liveboxandy/ZX-Spectrum-48K-Issue-3B---Based-on-Gerbers-by-PABB-on-PCBWay/STPS/CONN-TH_5P-P2.54_520315-5.step

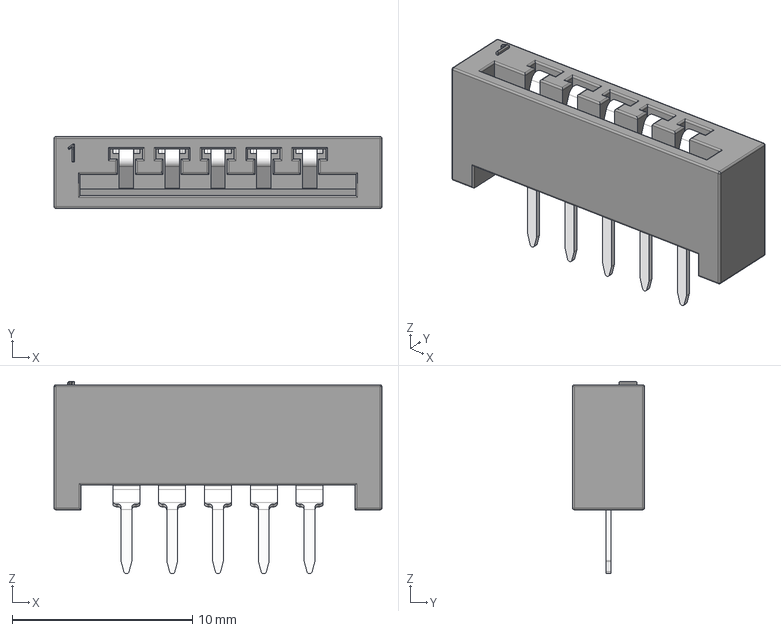
[picture p18: CAD file, 2026-09-27]
STPS/CONN-TH_5P-P2.54_520315-5.step
18.2 x 4.00 x 10.7 mm
Pins
Connector Body
