liveboxandy/ZX-Spectrum-48K-Issue-3B---Based-on-Gerbers-by-PABB-on-PCBWay/STPS/NS_LM1889N.step

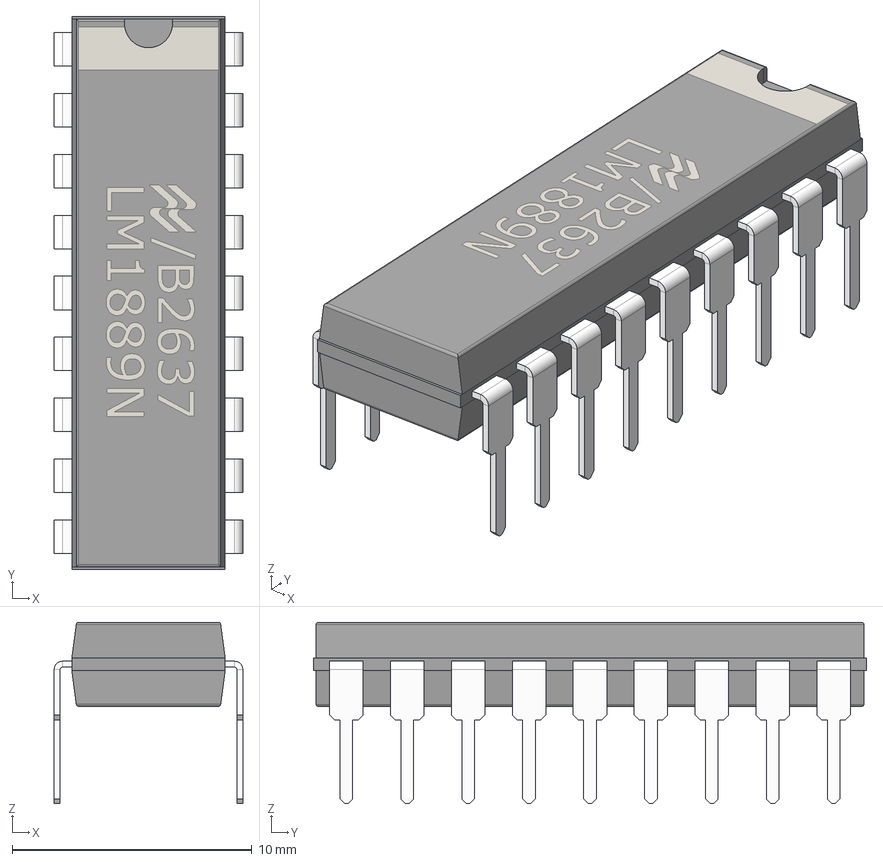
[picture p19: CAD file, 2026-09-27]
STPS/NS_LM1889N.step
7.87 x 23.1 x 7.57 mm
Basic - DIP 7.62 v3
DIP Pin 14-20 v3
DIP Pin 14-20 v3(Mirror)
