liveboxandy/ZX-Spectrum-48K-Issue-3B---Based-on-Gerbers-by-PABB-on-PCBWay/STPS/xAxial Capacitor.step

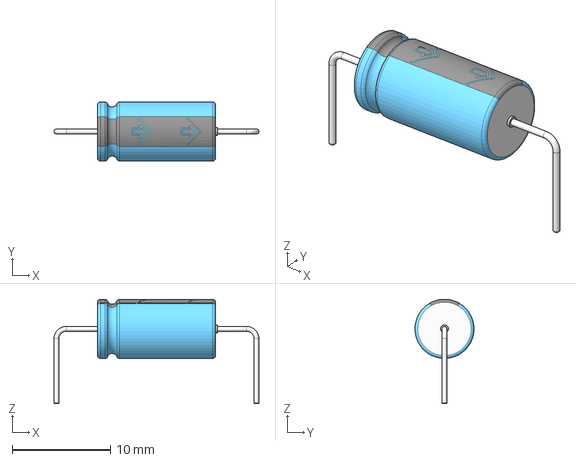
[picture p20: CAD file, 2026-09-27]
STPS/xAxial Capacitor.step
20.8 x 5.99 x 10.6 mm
