liveboxandy/ZX-Spectrum-48K-Issue-3B---Based-on-Gerbers-by-PABB-on-PCBWay/STPS/DO-35_3.90x1.90x0.60x10.16.STEP

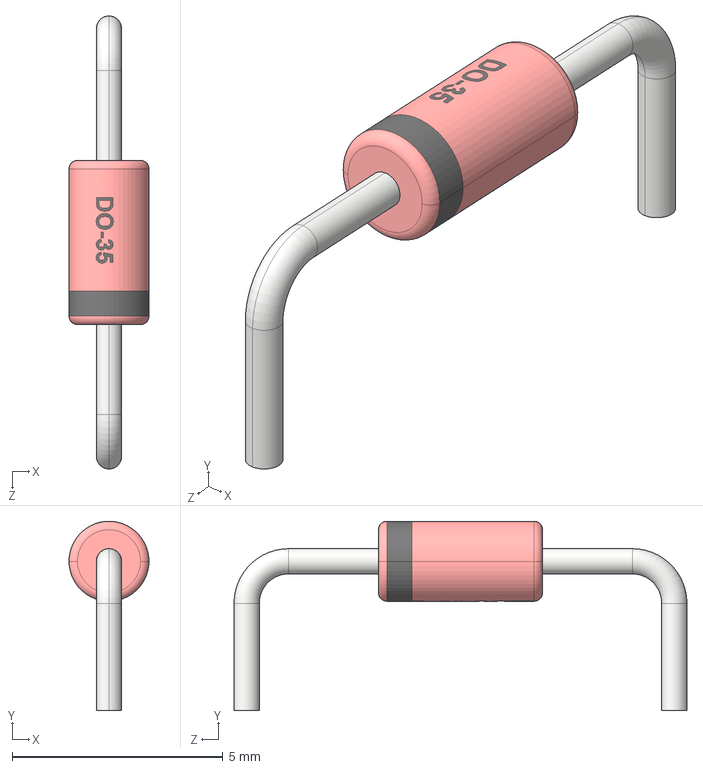
[picture p21: CAD file, 2026-09-27]
STPS/DO-35_3.90x1.90x0.60x10.16.STEP
1.90 x 4.50 x 10.8 mm
