liveboxandy/ZX-Spectrum-48K-Issue-3B---Based-on-Gerbers-by-PABB-on-PCBWay/STPS/DIP-24_W10.16mm_Socket.step

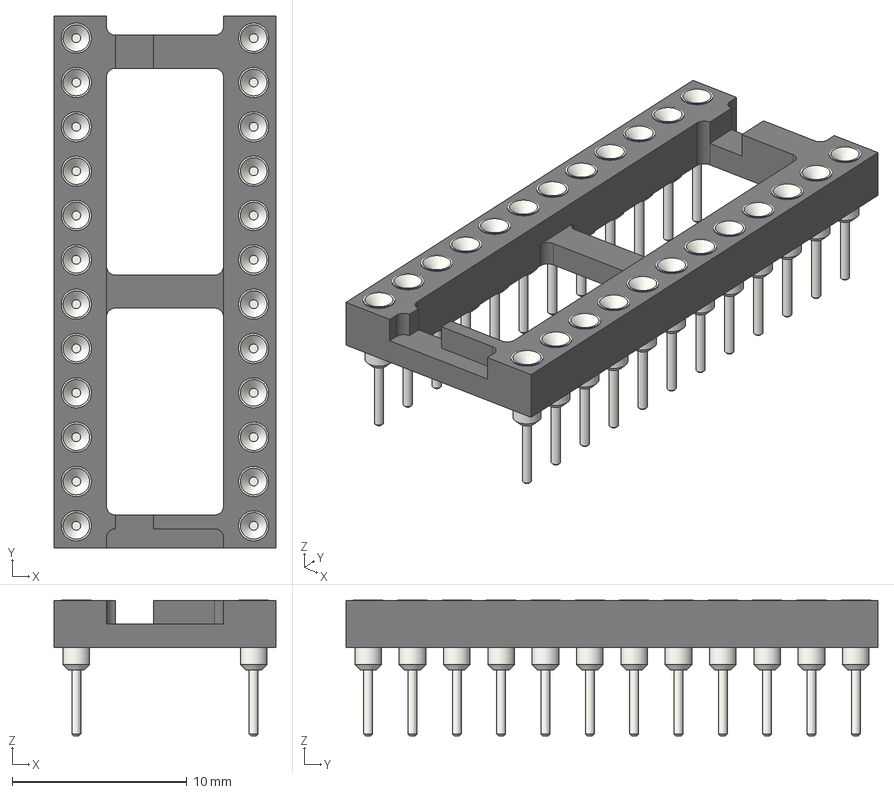
[picture p22: CAD file, 2026-09-27]
STPS/DIP-24_W10.16mm_Socket.step
12.7 x 30.5 x 7.79 mm
