liveboxandy/ZX-Spectrum-48K-Issue-3B---Based-on-Gerbers-by-PABB-on-PCBWay/STPS/Capacitor Ceramic No Polarity axial 22.86.STEP

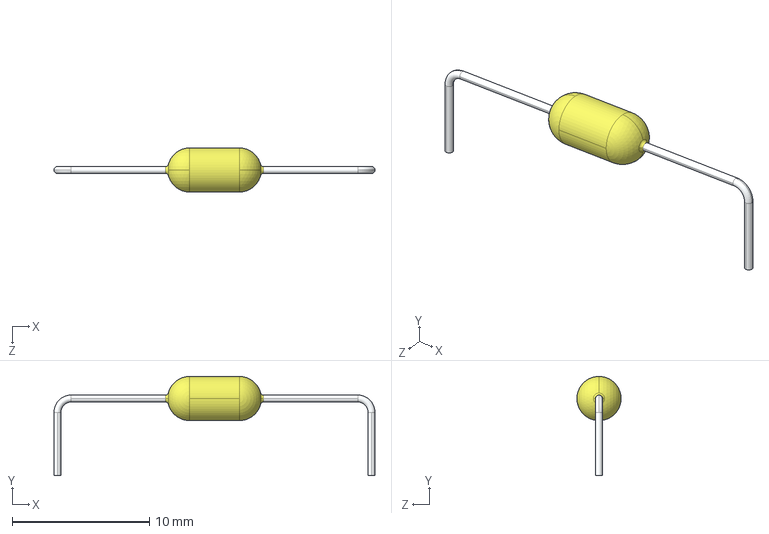
[picture p23: CAD file, 2026-09-27]
STPS/Capacitor Ceramic No Polarity axial 22.86.STEP
23.4 x 7.22 x 3.22 mm
