liveboxandy/ZX-Spectrum-48K-Issue-3B---Based-on-Gerbers-by-PABB-on-PCBWay/STPS/R_Axial_DIN0309_L9.0mm_D3.2mm_P12.70mm_Horizontal.step

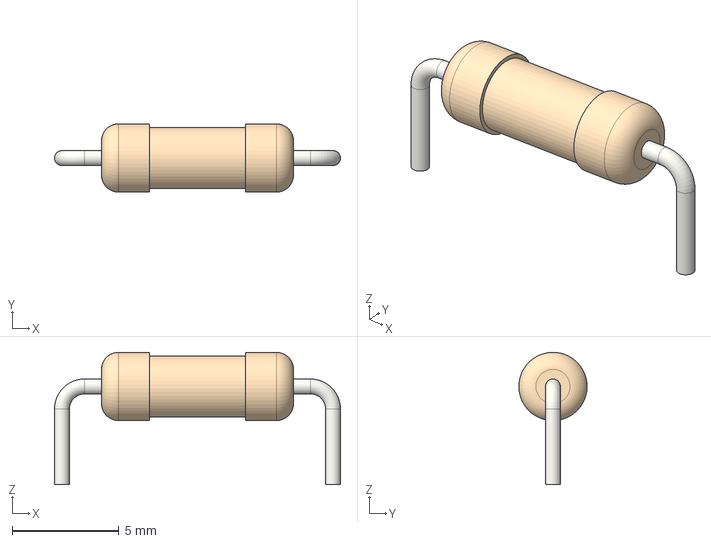
[picture p24: CAD file, 2026-09-27]
STPS/R_Axial_DIN0309_L9.0mm_D3.2mm_P12.70mm_Horizontal.step
13.4 x 3.20 x 6.20 mm
