liveboxandy/ZX-Spectrum-48K-Issue-3B---Based-on-Gerbers-by-PABB-on-PCBWay/STPS/409HS-1K.stp

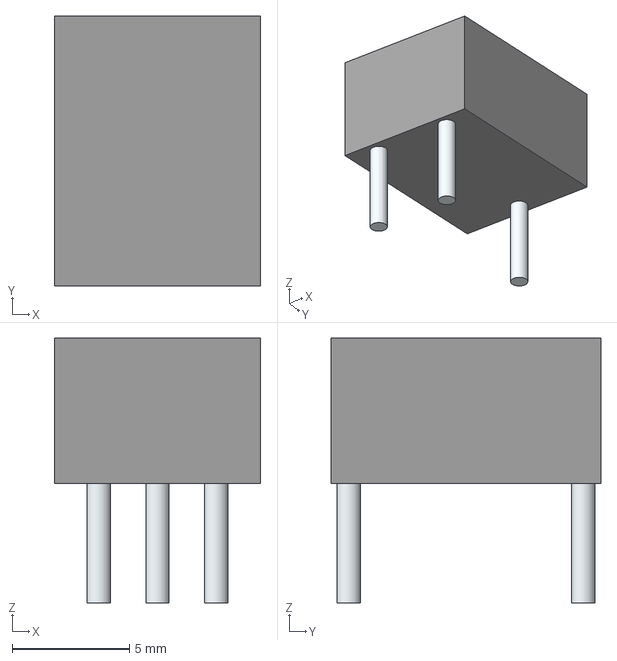
[picture p26: CAD file, 2026-09-27]
STPS/409HS-1K.stp
8.80 x 11.5 x 11.3 mm
Leads
