liveboxandy/ZX-Spectrum-48K-Issue-3B---Based-on-Gerbers-by-PABB-on-PCBWay/STPS/Resistor-0207-6.3x2.4x25.40.STEP

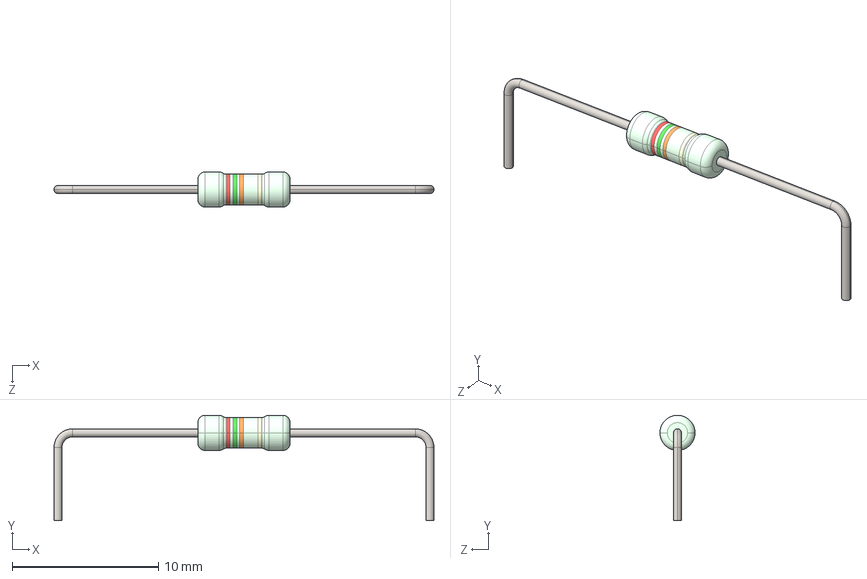
[picture p29: CAD file, 2026-09-27]
STPS/Resistor-0207-6.3x2.4x25.40.STEP
26.0 x 7.20 x 2.40 mm
