liveboxandy/ZX-Spectrum-48K-Issue-3B---Based-on-Gerbers-by-PABB-on-PCBWay/STPS/5-520315-5.stp

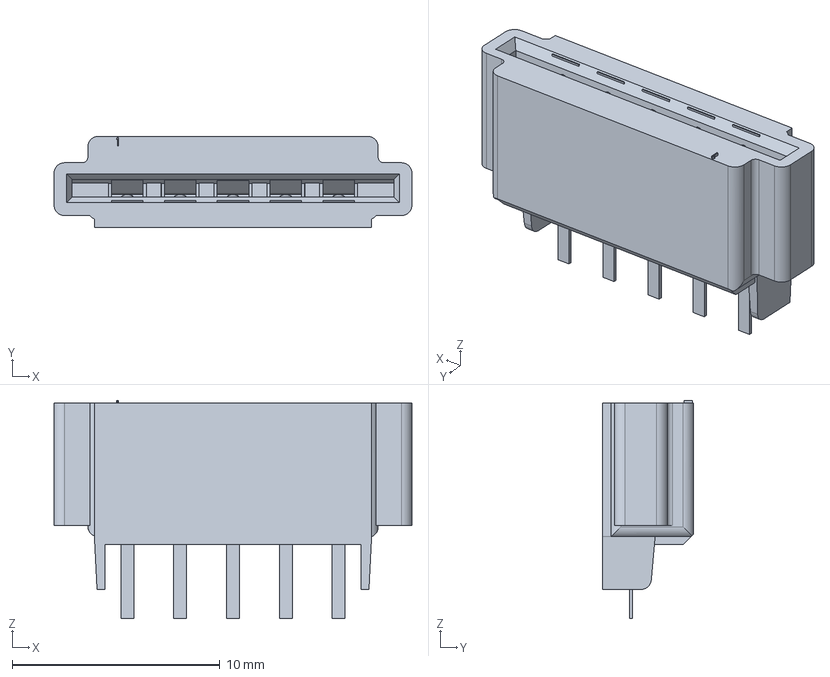
[picture p30: CAD file, 2026-09-27]
STPS/5-520315-5.stp
17.2 x 4.39 x 10.5 mm
