liveboxandy/ZX-Spectrum-48K-Issue-3B---Based-on-Gerbers-by-PABB-on-PCBWay/STPS/STC_4116.step

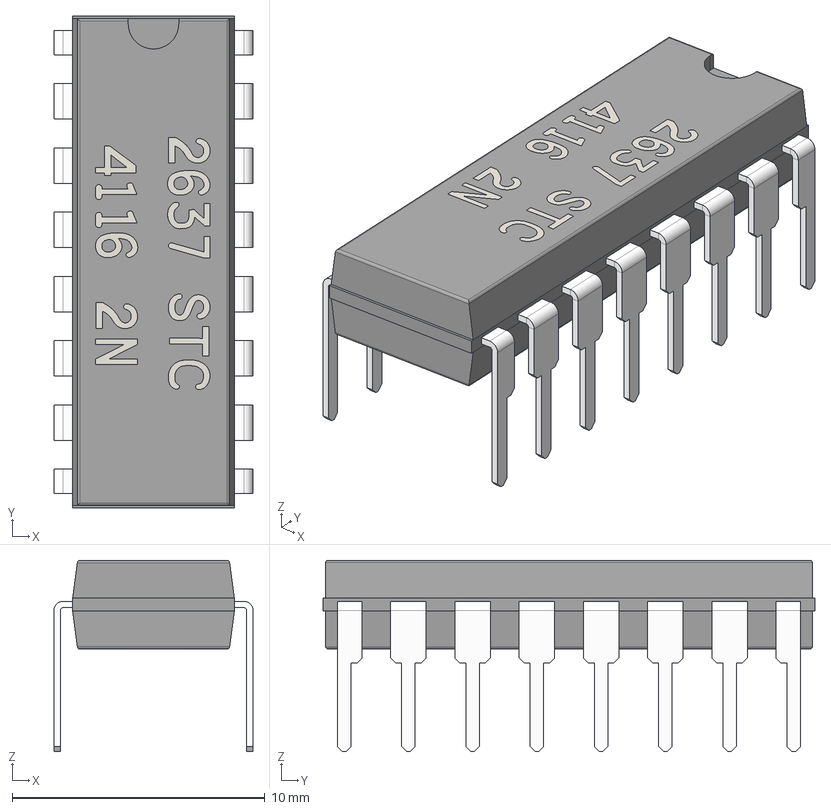
[picture p31: CAD file, 2026-09-27]
STPS/STC_4116.step
7.87 x 19.5 x 7.57 mm
Basic - DIP 7.62 v3
DIP Pin 14-20 v3
DIP Pin 14-20 v3(Mirror)
