liveboxandy/ZX-Spectrum-48K-Issue-3B---Based-on-Gerbers-by-PABB-on-PCBWay/STPS/CONN_5-520315-8_TYC.stp

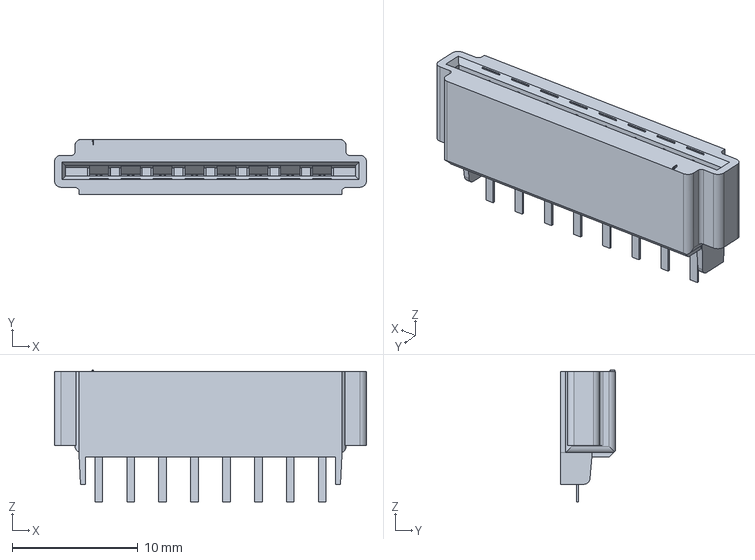
[picture p33: CAD file, 2026-09-27]
STPS/CONN_5-520315-8_TYC.stp
24.8 x 4.39 x 10.5 mm
