liveboxandy/ZX-Spectrum-48K-Issue-3B---Based-on-Gerbers-by-PABB-on-PCBWay/STPS/DO-35_3.90x1.90x0.60x22.86.STEP

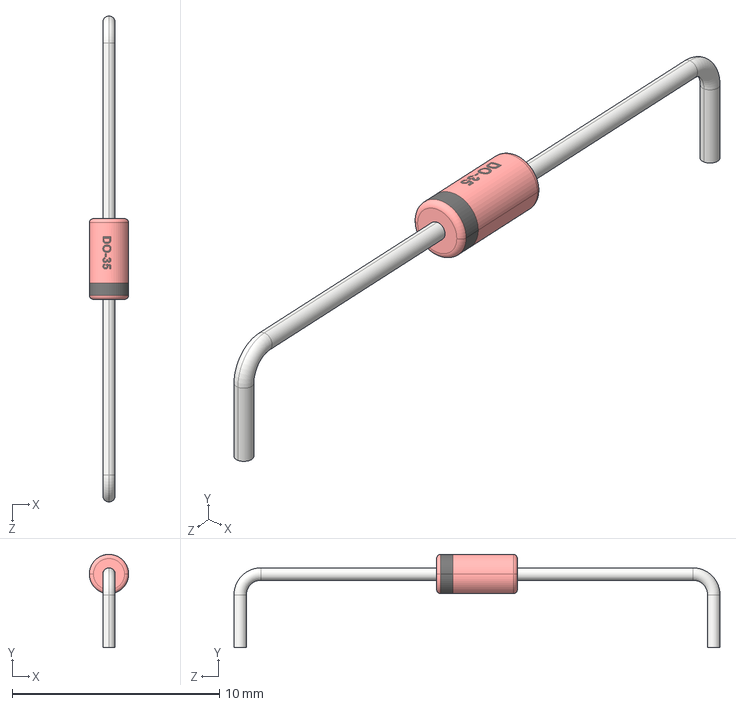
[picture p34: CAD file, 2026-09-27]
STPS/DO-35_3.90x1.90x0.60x22.86.STEP
1.90 x 4.50 x 23.5 mm
