liveboxandy/ZX-Spectrum-48K-Issue-3B---Based-on-Gerbers-by-PABB-on-PCBWay/STPS/Capacitor Ceramic No Polarity axial 10.16.STEP

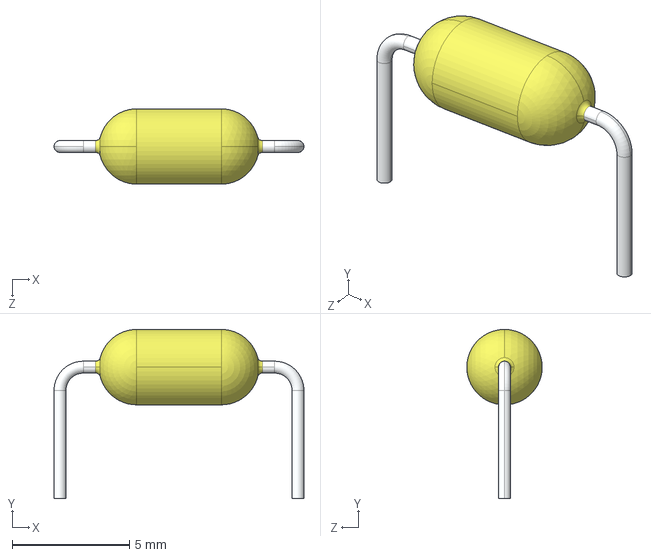
[picture p36: CAD file, 2026-09-27]
STPS/Capacitor Ceramic No Polarity axial 10.16.STEP
10.7 x 7.22 x 3.22 mm
