liveboxandy/ZX-Spectrum-48K-Issue-3B---Based-on-Gerbers-by-PABB-on-PCBWay/STPS/FCR1281 S6A 6mm.stp

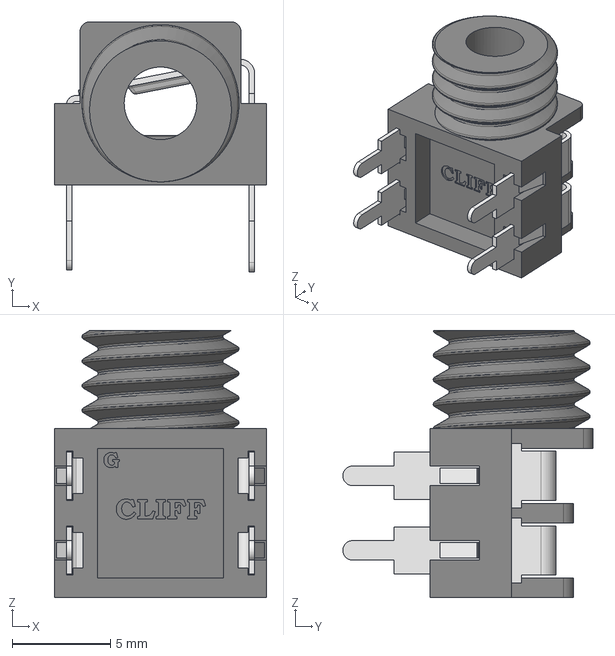
[picture p37: CAD file, 2026-09-27]
STPS/FCR1281 S6A 6mm.stp
10.8 x 12.8 x 13.6 mm
