liveboxandy/ZX-Spectrum-48K-Issue-3B---Based-on-Gerbers-by-PABB-on-PCBWay/STPS/DC Power Connector FC68148_20DC10A_202.1mm.STP

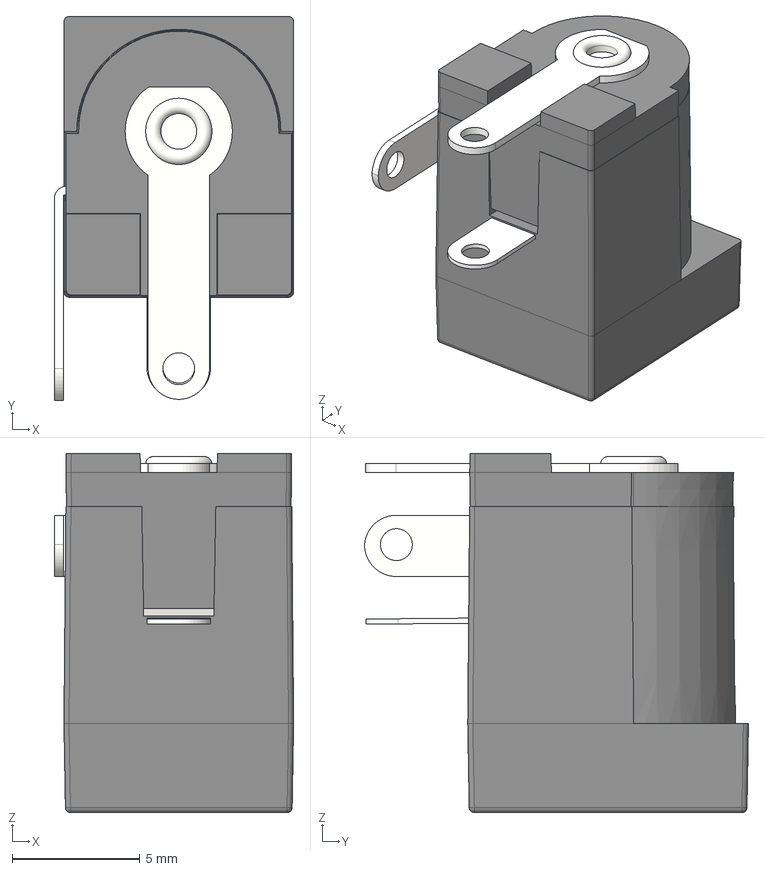
[picture p40: CAD file, 2026-09-27]
STPS/DC Power Connector FC68148_20DC10A_202.1mm.STP
9.37 x 15.0 x 14.1 mm
