liveboxandy/ZX-Spectrum-48K-Issue-3B---Based-on-Gerbers-by-PABB-on-PCBWay/STPS/DO-41-5.10x2.60x12.40.STEP

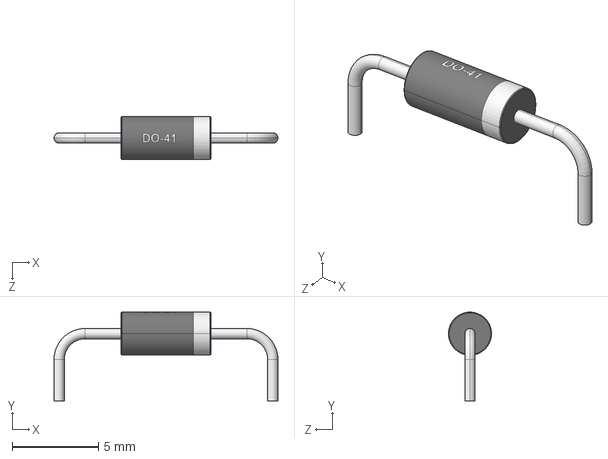
[picture p41: CAD file, 2026-09-27]
STPS/DO-41-5.10x2.60x12.40.STEP
13.0 x 5.15 x 2.50 mm
