liveboxandy/ZX-Spectrum-48K-Issue-3B---Based-on-Gerbers-by-PABB-on-PCBWay/STPS/Resistor-0414-11.5x4.5x25.40.STEP

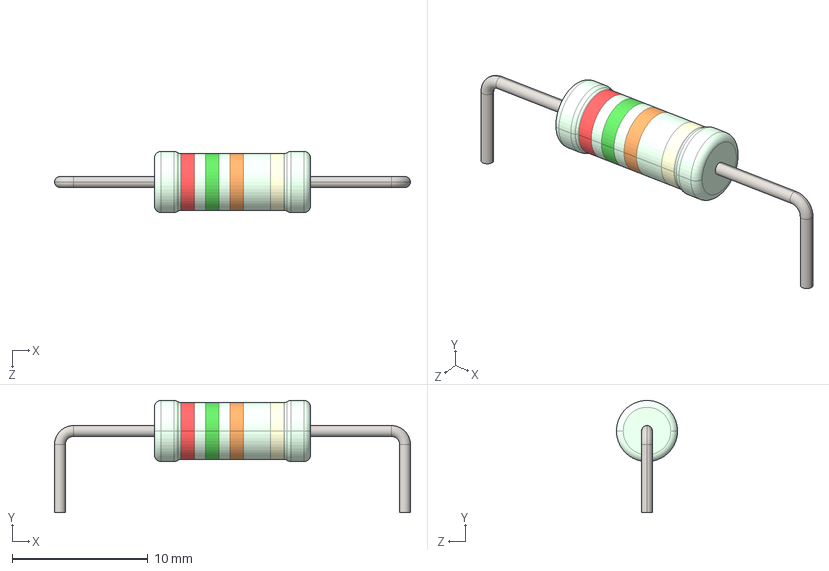
[picture p45: CAD file, 2026-09-27]
STPS/Resistor-0414-11.5x4.5x25.40.STEP
26.2 x 8.25 x 4.50 mm
