liveboxandy/ZX-Spectrum-48K-Issue-3B---Based-on-Gerbers-by-PABB-on-PCBWay/STPS/CP 13x5x0.5x17.78.STEP

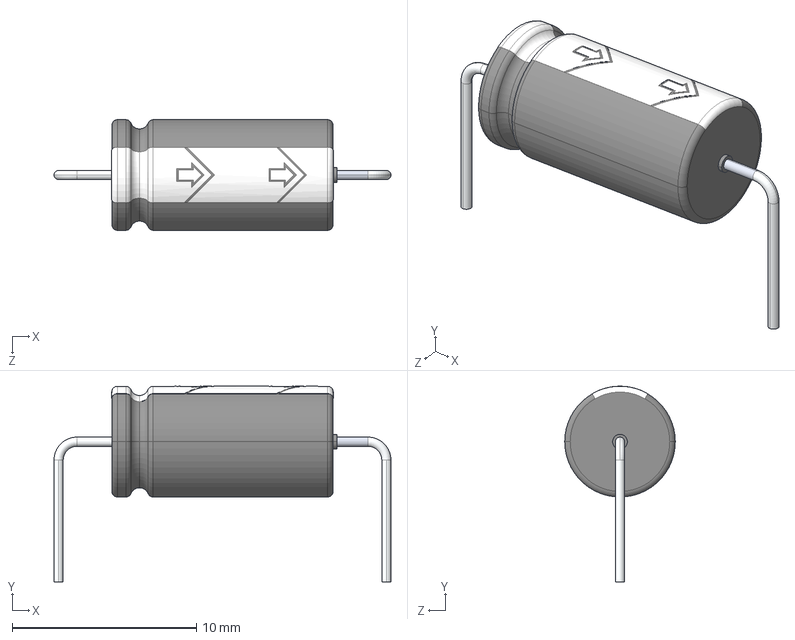
[picture p46: CAD file, 2026-09-27]
STPS/CP 13x5x0.5x17.78.STEP
18.3 x 10.6 x 6.00 mm
