liveboxandy/ZX-Spectrum-48K-Issue-3B---Based-on-Gerbers-by-PABB-on-PCBWay/STPS/Capacitor Ceramic No Polarity axial 17.72.STEP

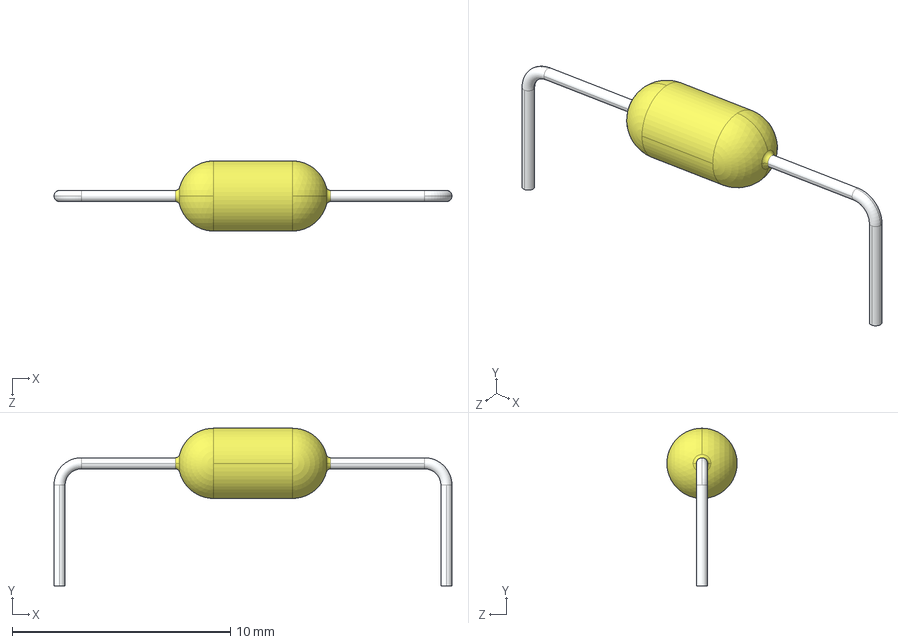
[picture p47: CAD file, 2026-09-27]
STPS/Capacitor Ceramic No Polarity axial 17.72.STEP
18.2 x 7.22 x 3.22 mm
