liveboxandy/ZX-Spectrum-48K-Issue-3B---Based-on-Gerbers-by-PABB-on-PCBWay/STPS/COIL_L1.step

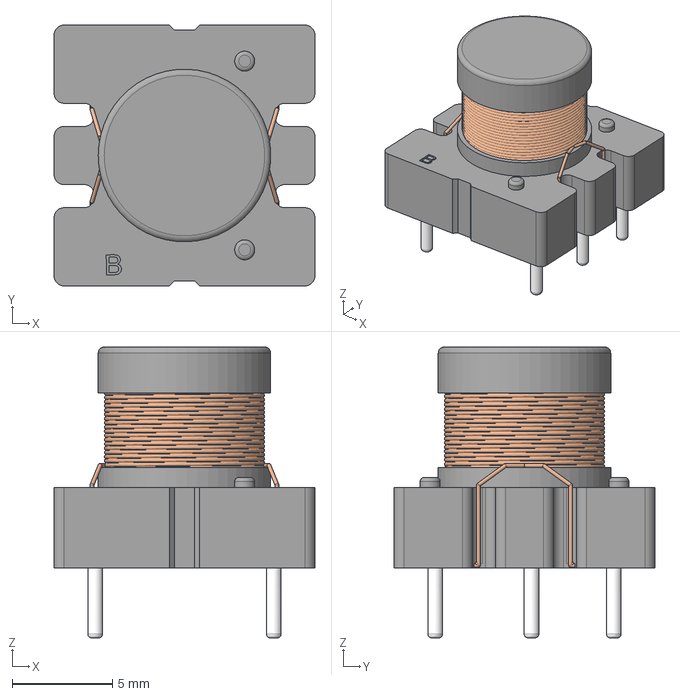
[picture p49: CAD file, 2026-09-27]
STPS/COIL_L1.step
13.0 x 13.0 x 14.5 mm
