liveboxandy/ZX-Spectrum-48K-Issue-3B---Based-on-Gerbers-by-PABB-on-PCBWay/STPS/Crystal-HC49-U.stp

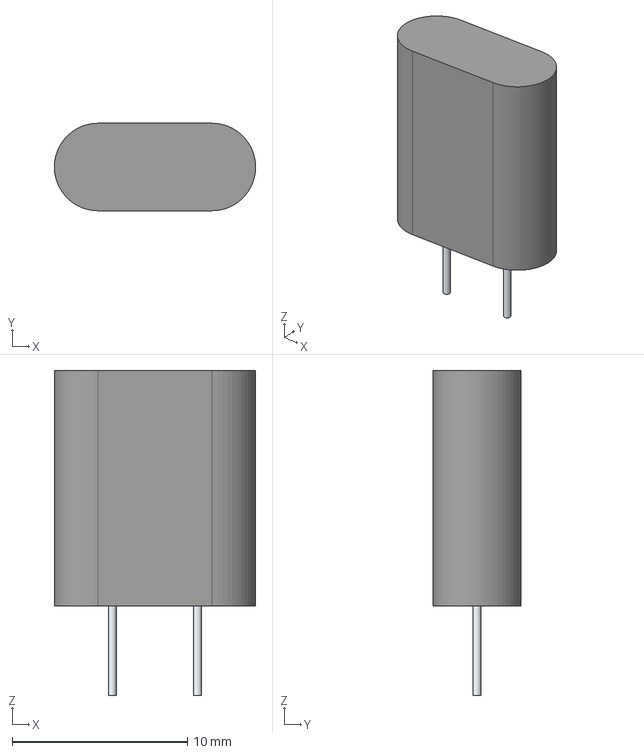
[picture p52: CAD file, 2026-09-27]
STPS/Crystal-HC49-U.stp
11.5 x 5.00 x 18.6 mm
Leads
