liveboxandy/ZX-Spectrum-48K-Issue-3B---Based-on-Gerbers-by-PABB-on-PCBWay/STPS/DO-41-5.10x2.60x22.86.STEP

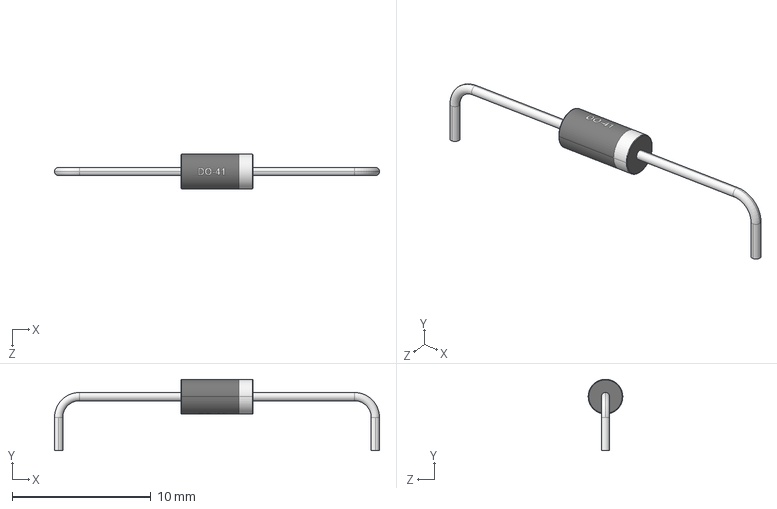
[picture p54: CAD file, 2026-09-27]
STPS/DO-41-5.10x2.60x22.86.STEP
23.5 x 5.15 x 2.50 mm
