liveboxandy/ZX-Spectrum-48K-Issue-3B---Based-on-Gerbers-by-PABB-on-PCBWay/STPS/Axial Capacitor.step

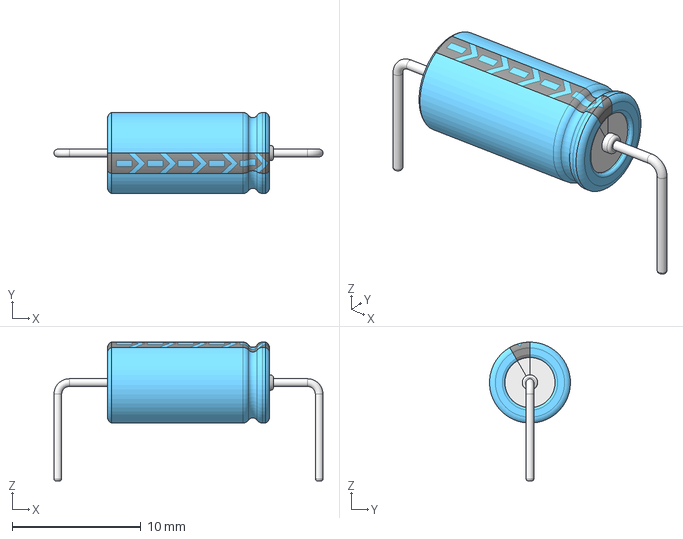
[picture p57: CAD file, 2026-09-27]
STPS/Axial Capacitor.step
20.9 x 6.29 x 10.8 mm
