liveboxandy/ZX-Spectrum-48K-Issue-3B---Based-on-Gerbers-by-PABB-on-PCBWay/STPS/PTC10LV10-103A2020.stp

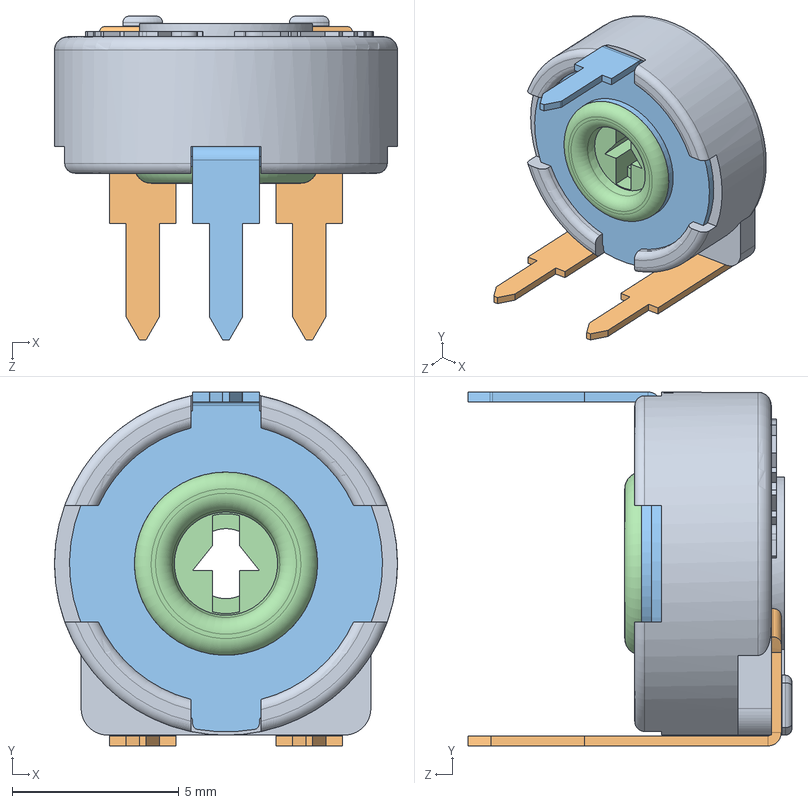
[picture p62: CAD file, 2026-09-27]
STPS/PTC10LV10-103A2020.stp
10.3 x 10.6 x 9.72 mm
PT10LV10-CARCASA
PT10LV10-TERMINAL DERECHO
PT10LV10-TERMINAL IZQUIERDO
PT10LV10-COLECTOR REBORDEADO
PT10LV10-PORTACURSOR_Predeterminada
