liveboxandy/ZX-Spectrum-48K-Issue-3B---Based-on-Gerbers-by-PABB-on-PCBWay/STPS/FERRANTI_ULA_6C001E-7.step

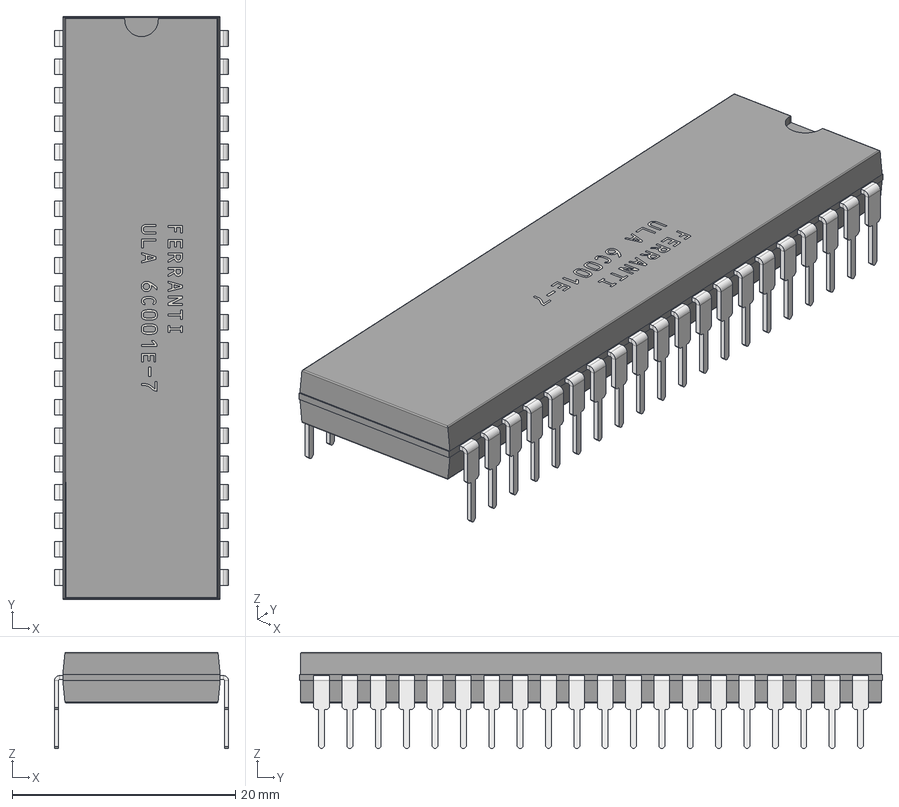
[picture p63: CAD file, 2026-09-27]
STPS/FERRANTI_ULA_6C001E-7.step
15.6 x 52.2 x 8.64 mm
Basic - DIP40 Wide v2
DIP Pin v2
DIP Pin v2(Mirror)
