liveboxandy/ZX-Spectrum-48K-Issue-3B---Based-on-Gerbers-by-PABB-on-PCBWay/STPS/Speaker.stp

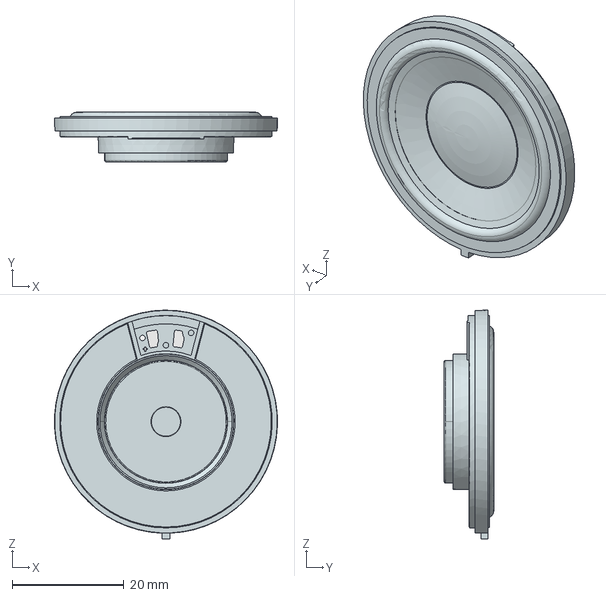
[picture p64: CAD file, 2026-09-27]
STPS/Speaker.stp
40.0 x 8.88 x 41.0 mm
