liveboxandy/ZX-Spectrum-48K-Issue-3B---Based-on-Gerbers-by-PABB-on-PCBWay/STPS/Var Cap BFC280831409.stp

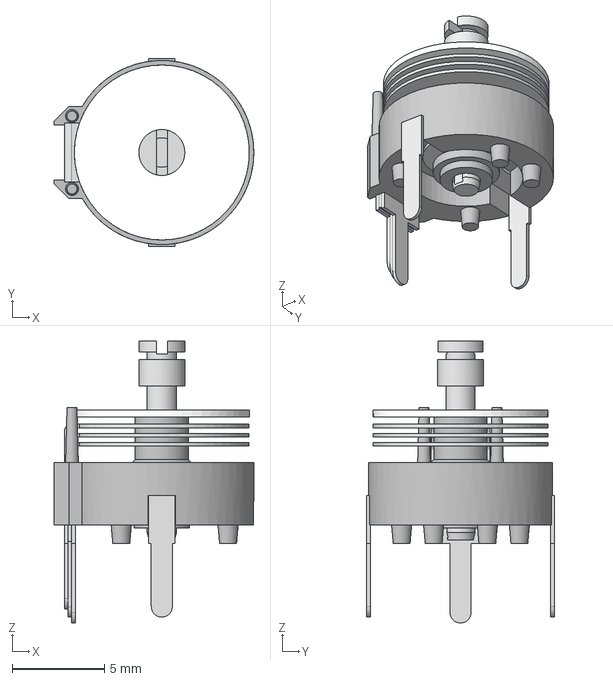
[picture p65: CAD file, 2026-09-27]
STPS/Var Cap BFC280831409.stp
10.8 x 10.2 x 15.3 mm
