liveboxandy/ZX-Spectrum-48K-Issue-3B---Based-on-Gerbers-by-PABB-on-PCBWay/STPS/PJ-322.step

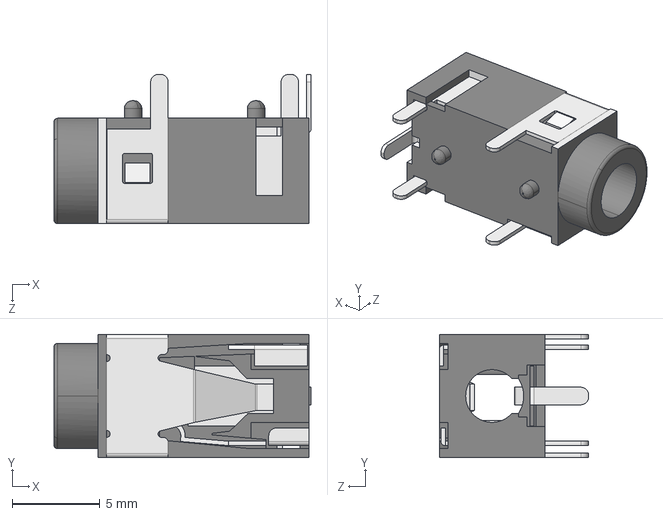
[picture p66: CAD file, 2026-09-27]
STPS/PJ-322.step
14.6 x 7.00 x 8.50 mm
