liveboxandy/ZX-Spectrum-48K-Issue-3B---Based-on-Gerbers-by-PABB-on-PCBWay/STPS/ZX Spectrum Speaker 40ohm.step

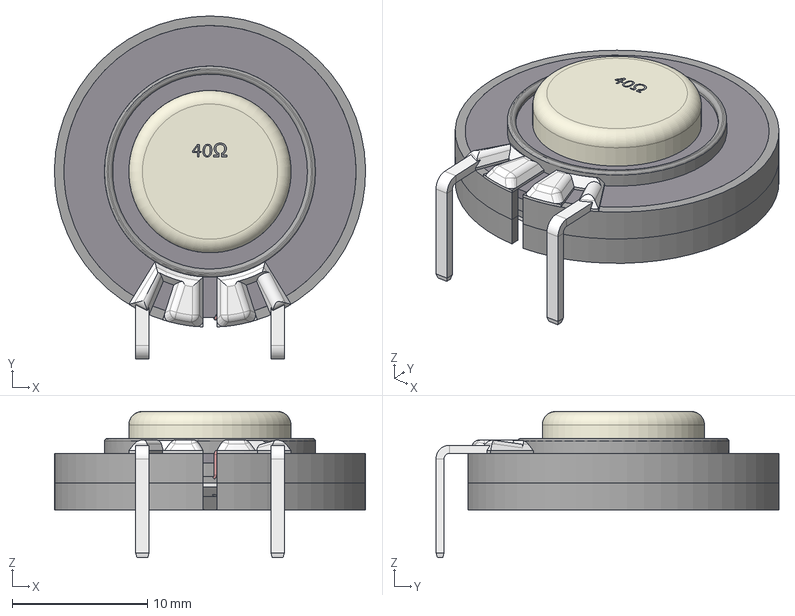
[picture p67: CAD file, 2026-09-27]
STPS/ZX Spectrum Speaker 40ohm.step
23.0 x 25.4 x 10.8 mm
Magnet
Plastic Cover
Board
CopperWire
Pins
