liveboxandy/ZX-Spectrum-48K-Issue-3B---Based-on-Gerbers-by-PABB-on-PCBWay/STPS/Resistor-0207-6.3x2.4x22.86.STEP

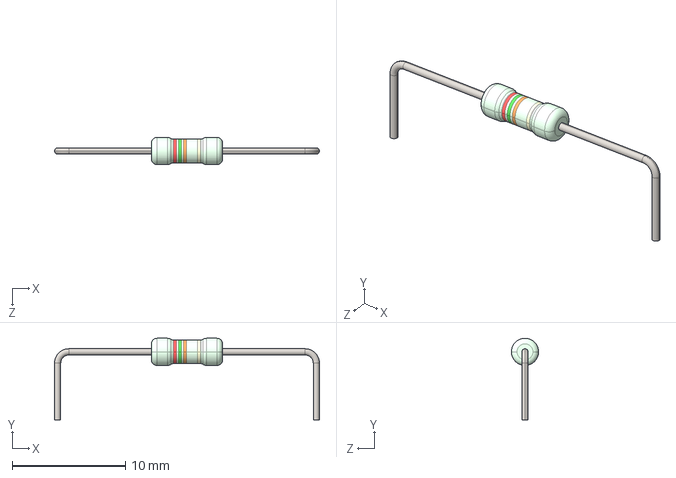
[picture p69: CAD file, 2026-09-27]
STPS/Resistor-0207-6.3x2.4x22.86.STEP
23.4 x 7.20 x 2.40 mm
