liveboxandy/ZX-Spectrum-48K-Issue-3B---Based-on-Gerbers-by-PABB-on-PCBWay/STPS/CMS-1805-24SP.stp

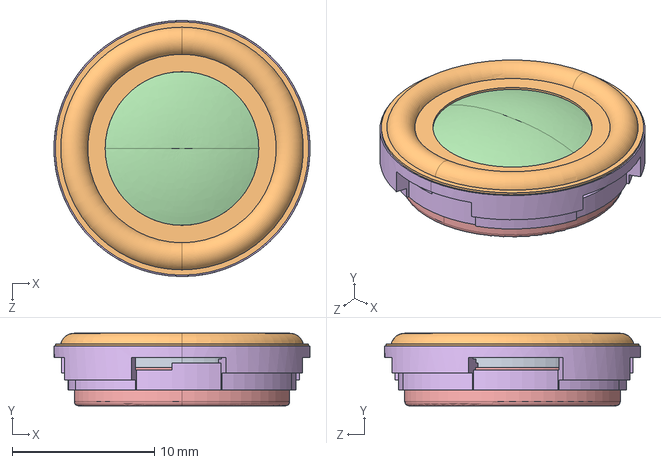
[picture p71: CAD file, 2026-09-27]
STPS/CMS-1805-24SP.stp
18.0 x 5.10 x 18.0 mm
