liveboxandy/ZX-Spectrum-48K-Issue-3B---Based-on-Gerbers-by-PABB-on-PCBWay/STPS/LM78xx_inc_Heatsink v6.step

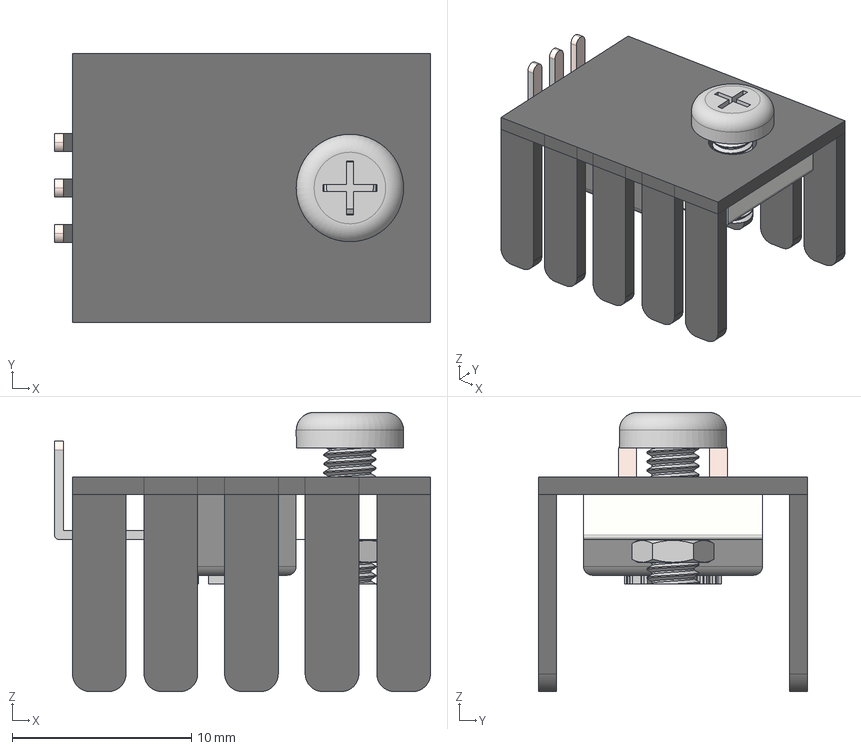
[picture p73: CAD file, 2026-09-27]
STPS/LM78xx_inc_Heatsink v6.step
21.0 x 15.0 x 15.6 mm
