liveboxandy/ZX-Spectrum-48K-Issue-3B---Based-on-Gerbers-by-PABB-on-PCBWay/STPS/TO220 Horizontal - Bent Leads.STEP

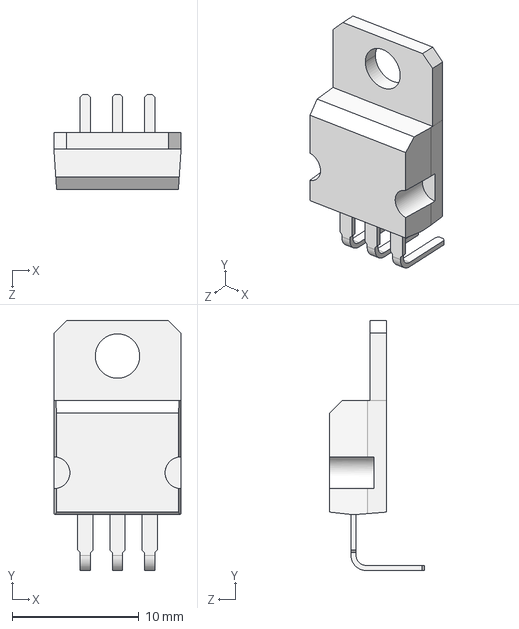
[picture p74: CAD file, 2026-09-27]
STPS/TO220 Horizontal - Bent Leads.STEP
10.0 x 19.7 x 7.50 mm
