liveboxandy/ZX-Spectrum-48K-Issue-3B---Based-on-Gerbers-by-PABB-on-PCBWay/STPS/Jumper.step

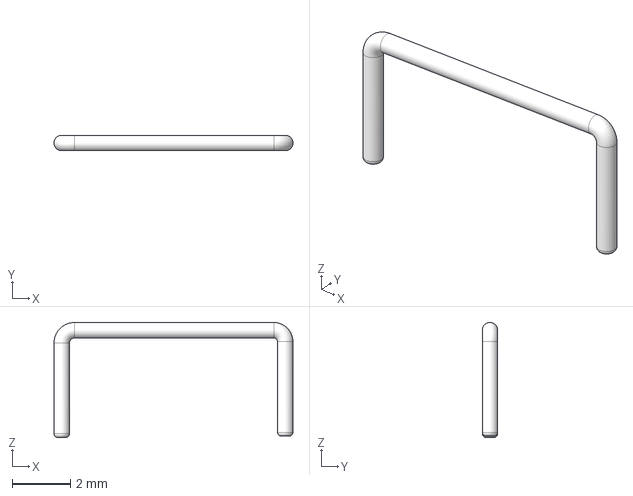
[picture p76: CAD file, 2026-09-27]
STPS/Jumper.step
8.18 x 0.53 x 3.94 mm
