liveboxandy/ZX-Spectrum-48K-Issue-3B---Based-on-Gerbers-by-PABB-on-PCBWay/STPS/Resistor-0414-11.5x4.5x20.32.STEP

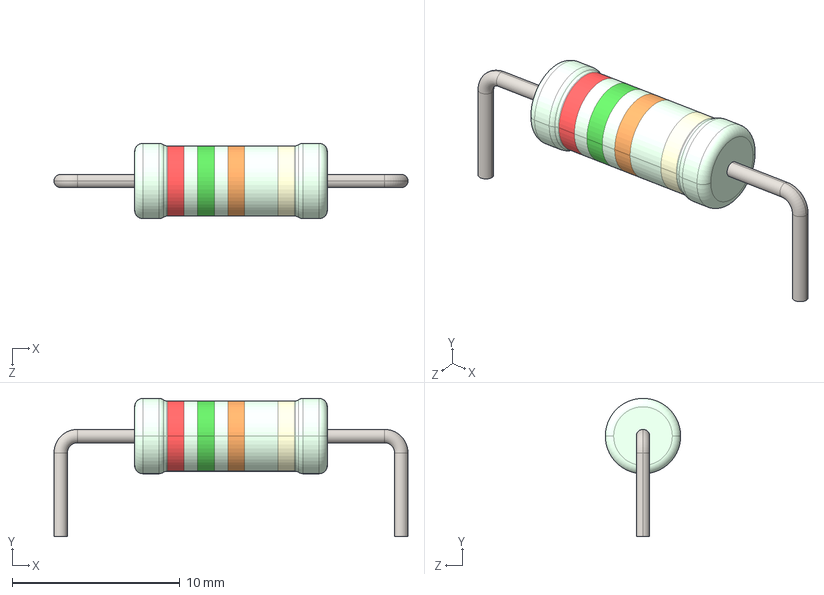
[picture p77: CAD file, 2026-09-27]
STPS/Resistor-0414-11.5x4.5x20.32.STEP
21.1 x 8.25 x 4.50 mm
