liveboxandy/ZX-Spectrum-48K-Issue-3B---Based-on-Gerbers-by-PABB-on-PCBWay/STPS/AUDIO_JACK_3PIN.step

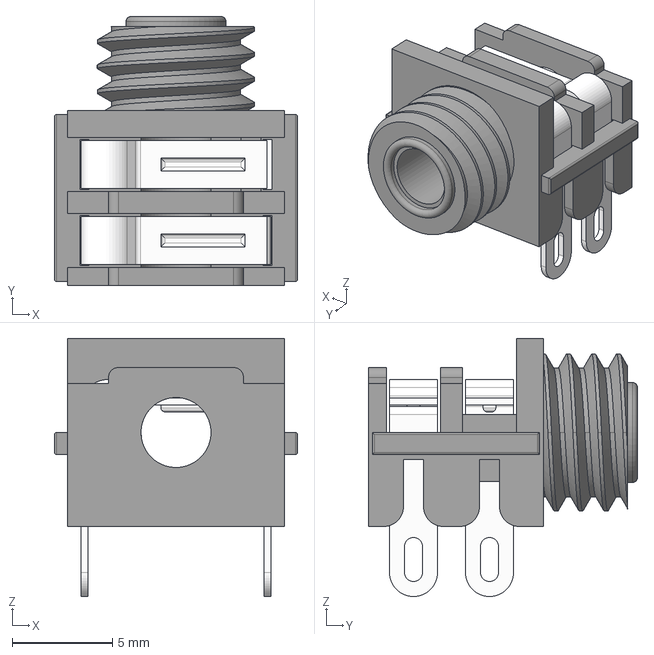
[picture p79: CAD file, 2026-09-27]
STPS/AUDIO_JACK_3PIN.step
12.2 x 13.4 x 12.9 mm
Pins
Plastic Body
