liveboxandy/ZX-Spectrum-48K-Issue-3B---Based-on-Gerbers-by-PABB-on-PCBWay/STPS/13.34x13.34 Bobin.STEP

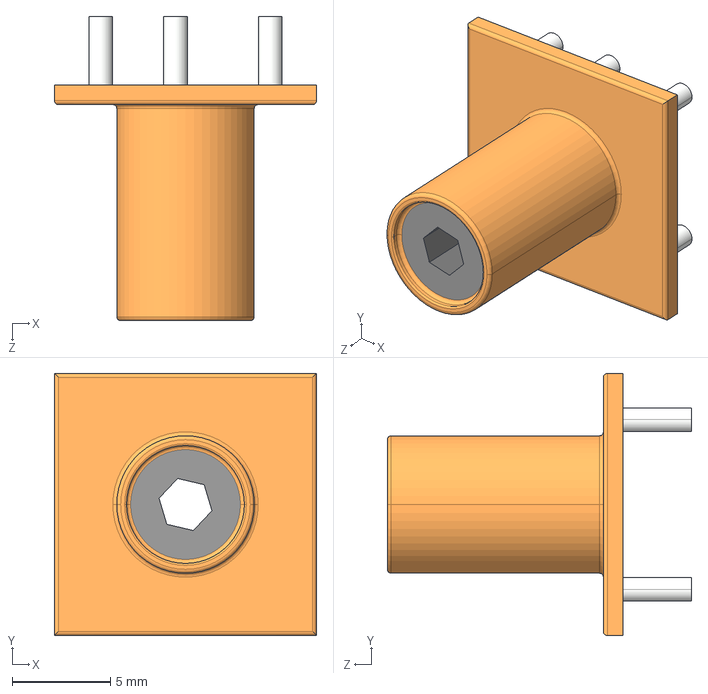
[picture p80: CAD file, 2026-08-16]
STPS/13.34x13.34 Bobin.STEP
13.3 x 13.3 x 15.5 mm
