liveboxandy/ZX-Spectrum-48K-Issue-3B---Based-on-Gerbers-by-PABB-on-PCBWay/STPS/Capacitor Ceramic No Polarity axial 12.70.STEP

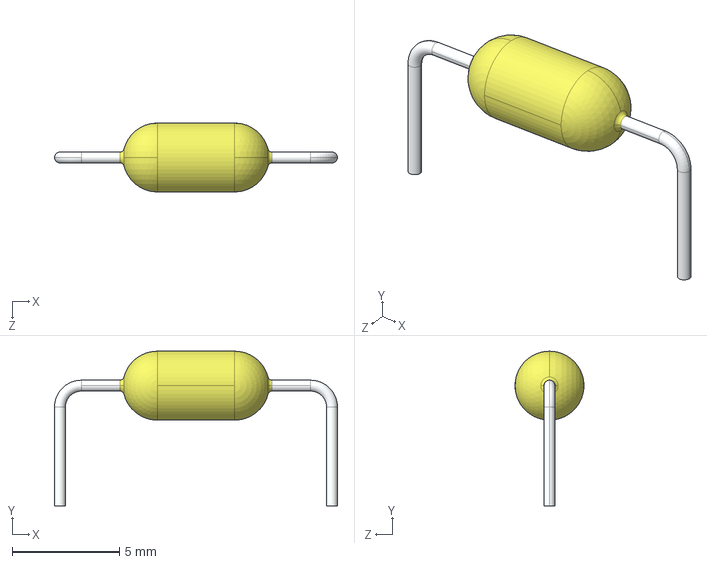
[picture p82: CAD file, 2026-08-16]
STPS/Capacitor Ceramic No Polarity axial 12.70.STEP
13.2 x 7.22 x 3.22 mm
