liveboxandy/ZX-Spectrum-48K-Issue-3B---Based-on-Gerbers-by-PABB-on-PCBWay/STPS/DIP-14_W7.62mm.step

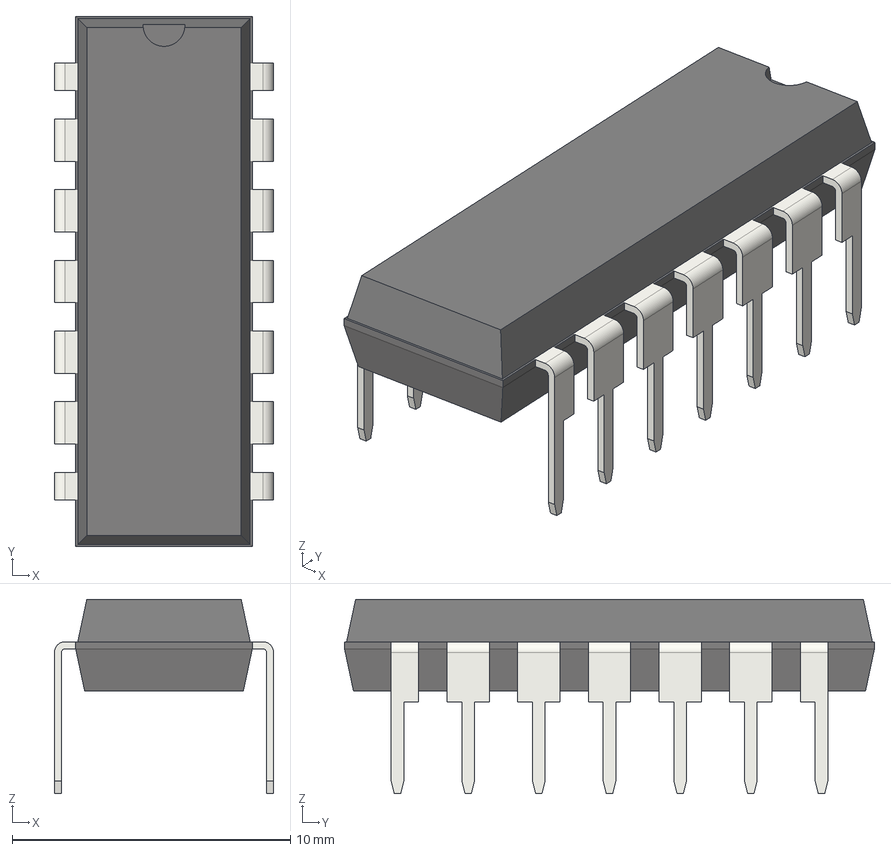
[picture p83: CAD file, 2026-08-16]
STPS/DIP-14_W7.62mm.step
7.87 x 19.1 x 6.98 mm
