liveboxandy/ZX-Spectrum-48K-Issue-3B---Based-on-Gerbers-by-PABB-on-PCBWay/STPS/22-02-3053.stp

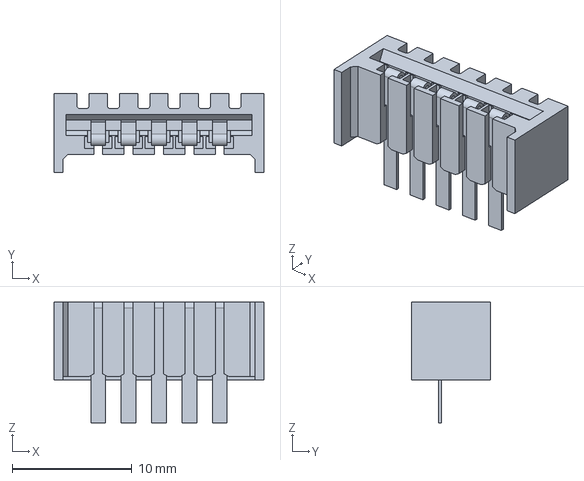
[picture p84: CAD file, 2026-08-16]
STPS/22-02-3053.stp
17.6 x 6.60 x 10.1 mm
