liveboxandy/ZX-Spectrum-48K-Issue-3B---Based-on-Gerbers-by-PABB-on-PCBWay/STPS/Crystal-HC18-U RA.STEP

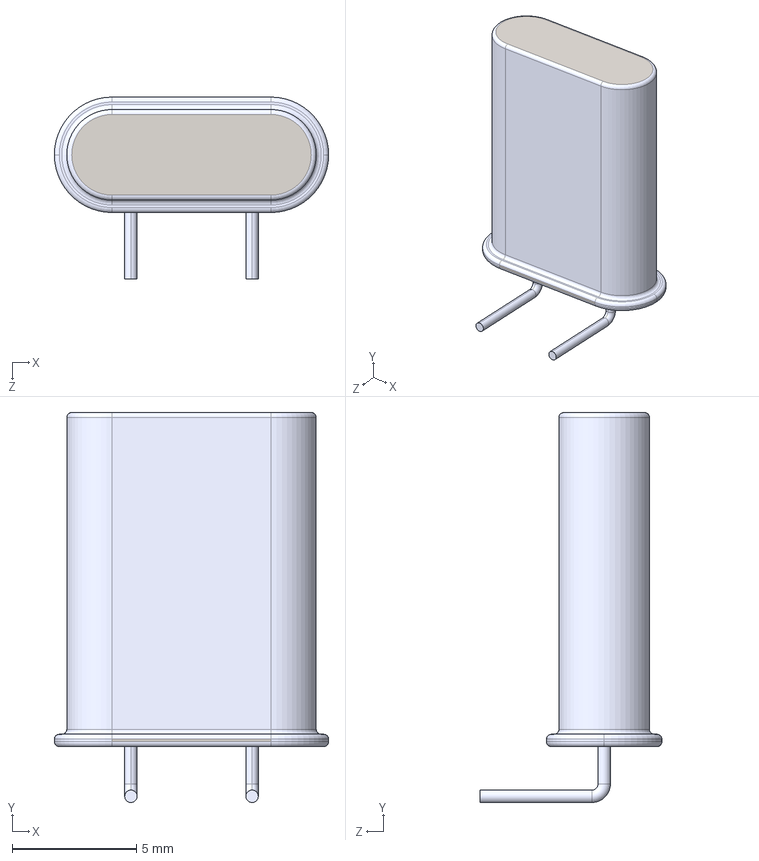
[picture p85: CAD file, 2026-08-16]
STPS/Crystal-HC18-U RA.STEP
11.1 x 15.7 x 7.32 mm
