liveboxandy/ZX-Spectrum-48K-Issue-3B---Based-on-Gerbers-by-PABB-on-PCBWay/STPS/TO-220-2_Horizontal_TabUp.step

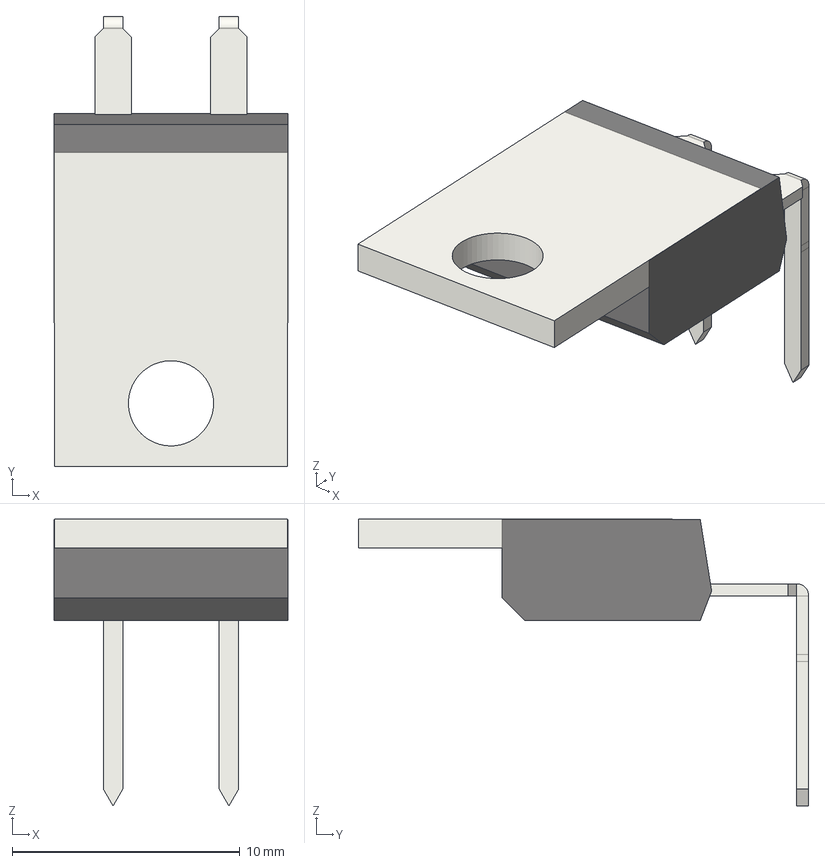
[picture p87: CAD file, 2026-08-16]
STPS/TO-220-2_Horizontal_TabUp.step
10.2 x 19.7 x 12.6 mm
