liveboxandy/ZX-Spectrum-48K-Issue-3B---Based-on-Gerbers-by-PABB-on-PCBWay/STPS/Transistor Kinked Lead.stp

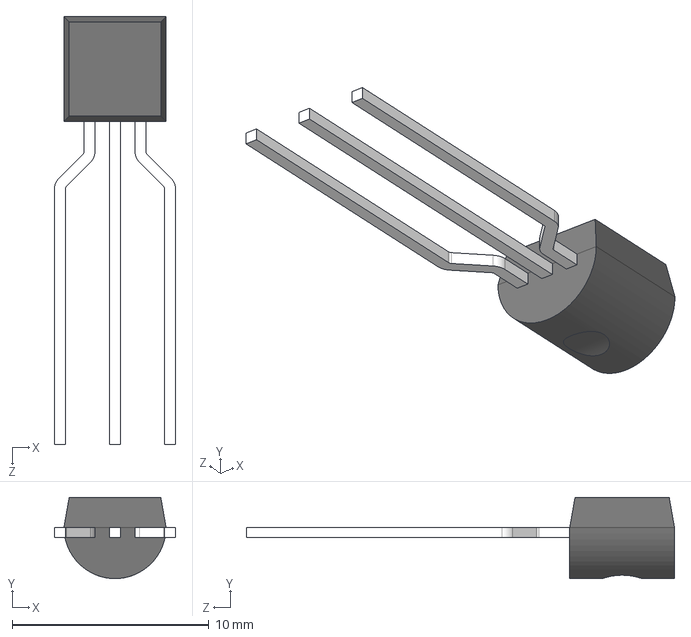
[picture p89: CAD file, 2026-08-16]
STPS/Transistor Kinked Lead.stp
6.16 x 4.13 x 21.8 mm
