liveboxandy/ZX-Spectrum-48K-Issue-3B---Based-on-Gerbers-by-PABB-on-PCBWay/STPS/Crystal-Low.stp

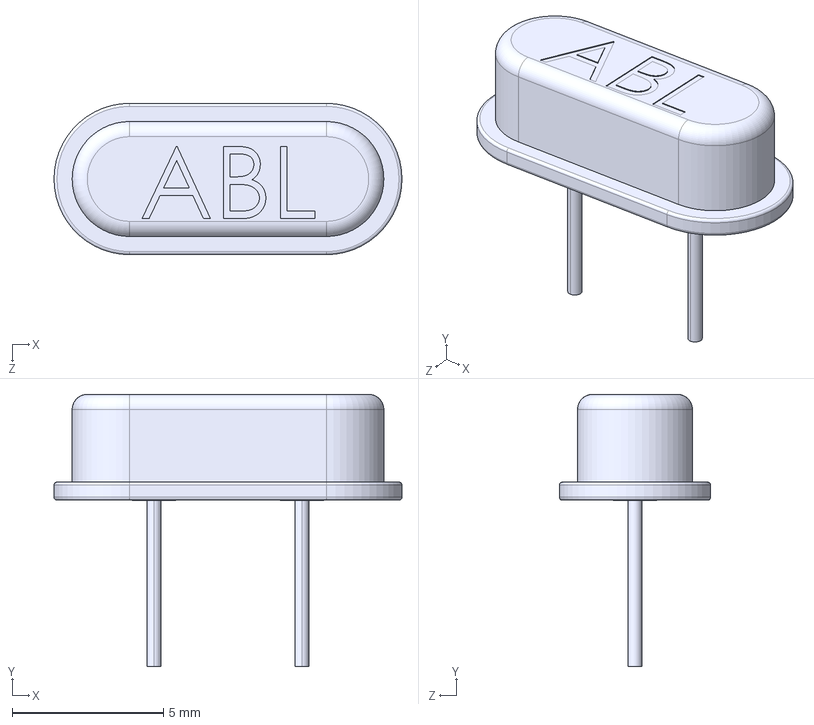
[picture p91: CAD file, 2026-08-16]
STPS/Crystal-Low.stp
11.5 x 9.00 x 5.00 mm
