liveboxandy/ZX-Spectrum-48K-Issue-3B---Based-on-Gerbers-by-PABB-on-PCBWay/STPS/WireLink 7.62mm 1430-3.STEP

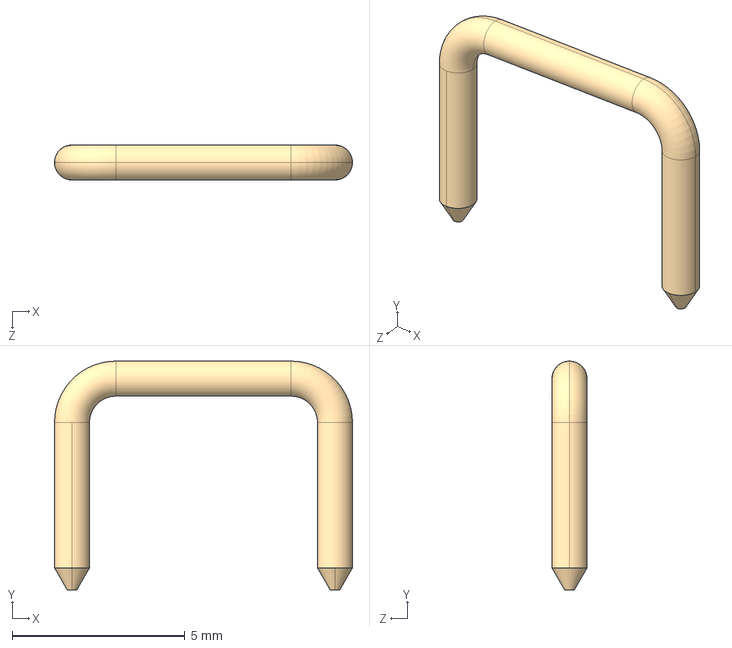
[picture p92: CAD file, 2026-08-16]
STPS/WireLink 7.62mm 1430-3.STEP
8.64 x 6.63 x 1.02 mm
