liveboxandy/ZX-Spectrum-48K-Issue-3B---Based-on-Gerbers-by-PABB-on-PCBWay/STPS/Resistor-0207-6.3x2.4x12.40.STEP

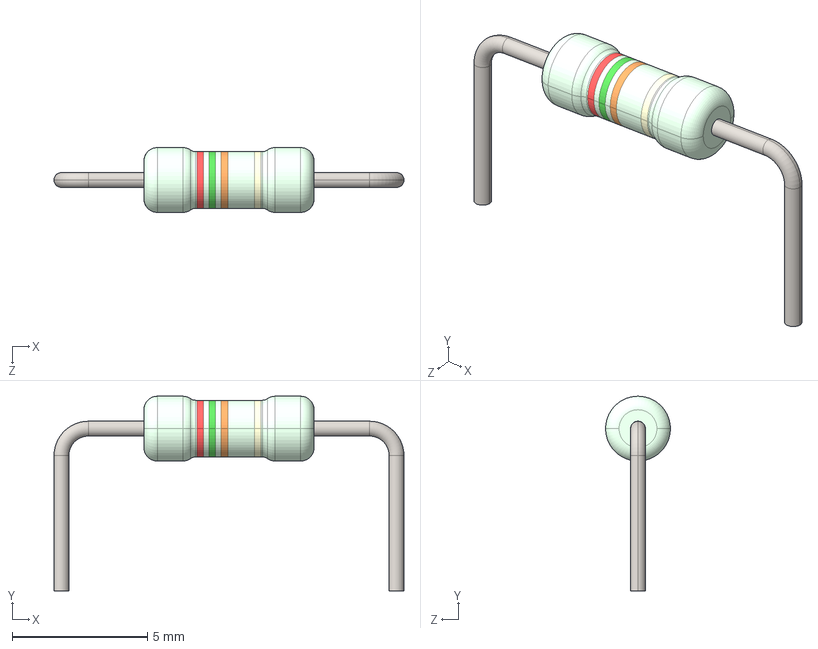
[picture p93: CAD file, 2026-08-16]
STPS/Resistor-0207-6.3x2.4x12.40.STEP
13.0 x 7.20 x 2.40 mm
