liveboxandy/ZX-Spectrum-48K-Issue-3B---Based-on-Gerbers-by-PABB-on-PCBWay/STPS/DO-35_3.90x1.90x0.60x12.70.STEP

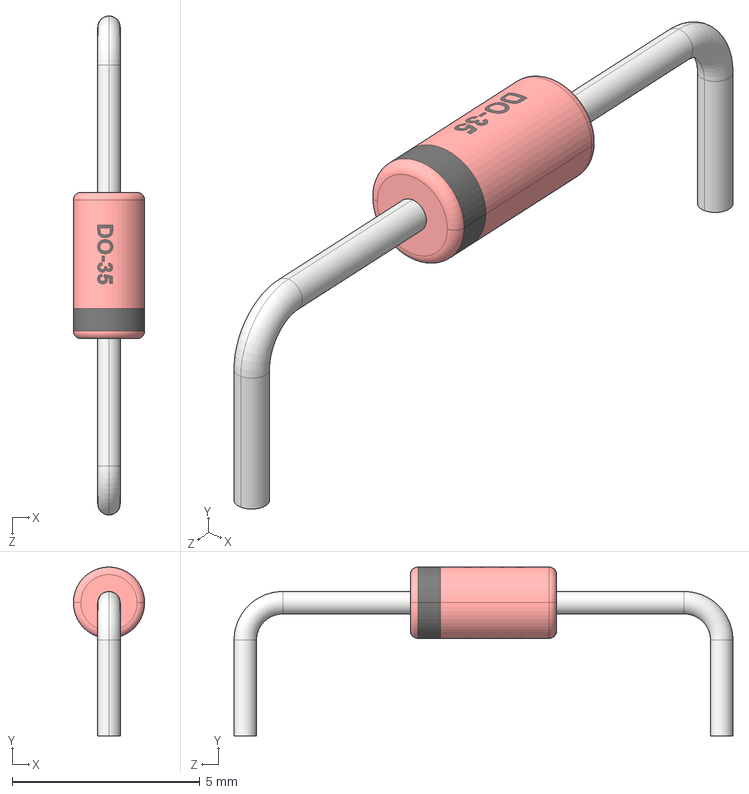
[picture p95: CAD file, 2026-08-16]
STPS/DO-35_3.90x1.90x0.60x12.70.STEP
1.90 x 4.50 x 13.3 mm
