liveboxandy/ZX-Spectrum-48K-Issue-3B---Based-on-Gerbers-by-PABB-on-PCBWay/STPS/DIP-28_W15.24mm_Socket.step

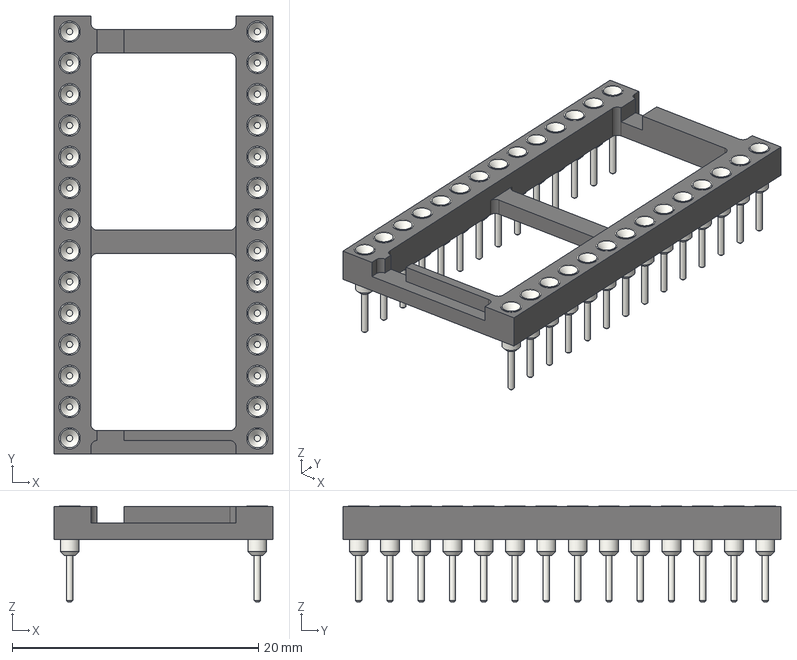
[picture p96: CAD file, 2026-08-16]
STPS/DIP-28_W15.24mm_Socket.step
17.8 x 35.6 x 7.79 mm
