liveboxandy/ZX-Spectrum-48K-Issue-3B---Based-on-Gerbers-by-PABB-on-PCBWay/STPS/DIP-28_W15.24mm.step

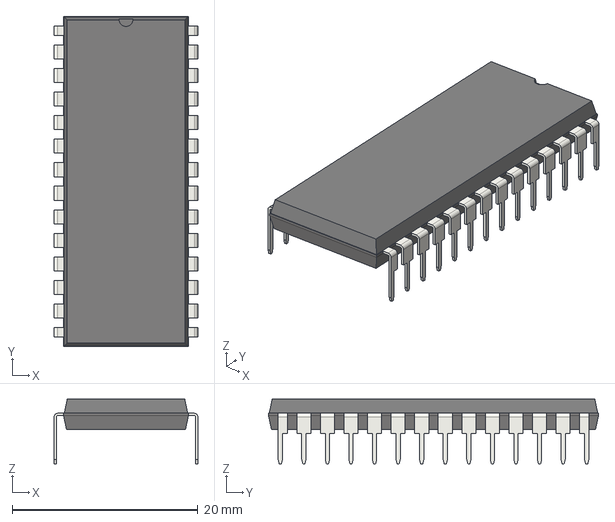
[picture p97: CAD file, 2026-08-16]
STPS/DIP-28_W15.24mm.step
15.5 x 35.6 x 6.98 mm
