liveboxandy/ZX-Spectrum-48K-Issue-3B---Based-on-Gerbers-by-PABB-on-PCBWay/STPS/Resistor-0414-11.5x4.5x22.86.STEP

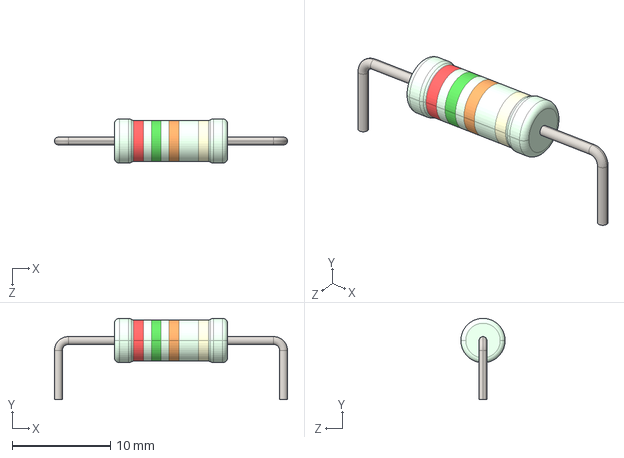
[picture p99: CAD file, 2026-08-16]
STPS/Resistor-0414-11.5x4.5x22.86.STEP
23.7 x 8.25 x 4.50 mm
