liveboxandy/ZX-Spectrum-48K-Issue-3B---Based-on-Gerbers-by-PABB-on-PCBWay/STPS/22-02-3083.stp

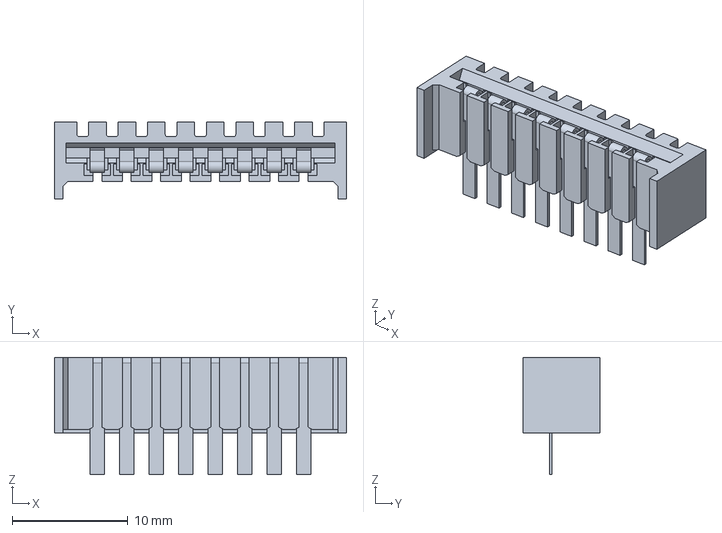
[picture p100: CAD file, 2026-08-16]
STPS/22-02-3083.stp
25.2 x 6.60 x 10.1 mm
