liveboxandy/ZX-Spectrum-48K-Issue-3B---Based-on-Gerbers-by-PABB-on-PCBWay/STPS/TO-92S_Normal_LF42_rev1.0.STEP

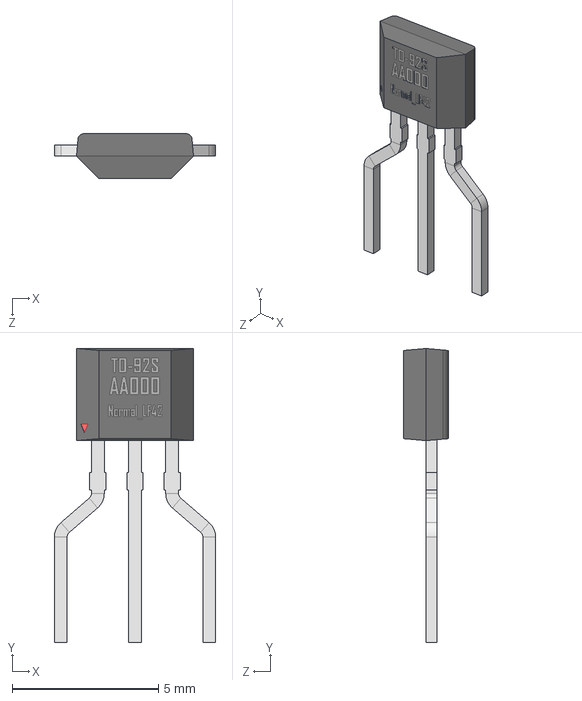
[picture p101: CAD file, 2026-08-16]
STPS/TO-92S_Normal_LF42_rev1.0.STEP
5.52 x 10.1 x 1.52 mm
