liveboxandy/ZX-Spectrum-48K-Issue-3B---Based-on-Gerbers-by-PABB-on-PCBWay/STPS/Speaker SM230332-2.stp

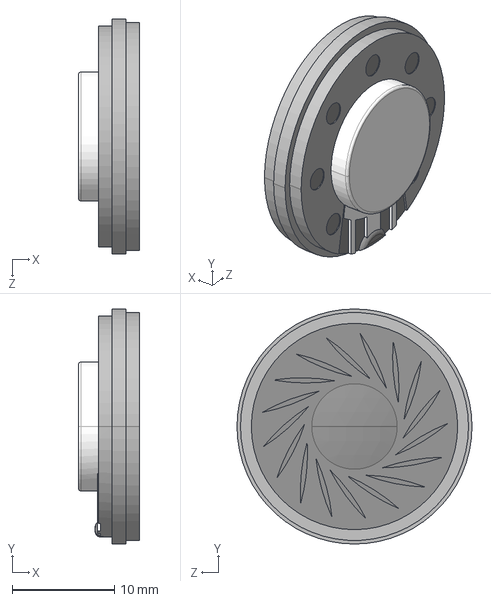
[picture p102: CAD file, 2026-08-16]
STPS/Speaker SM230332-2.stp
6.00 x 23.0 x 23.0 mm
