liveboxandy/ZX-Spectrum-48K-Issue-3B---Based-on-Gerbers-by-PABB-on-PCBWay/STPS/DIP-18_W7.62mm_Socket.step

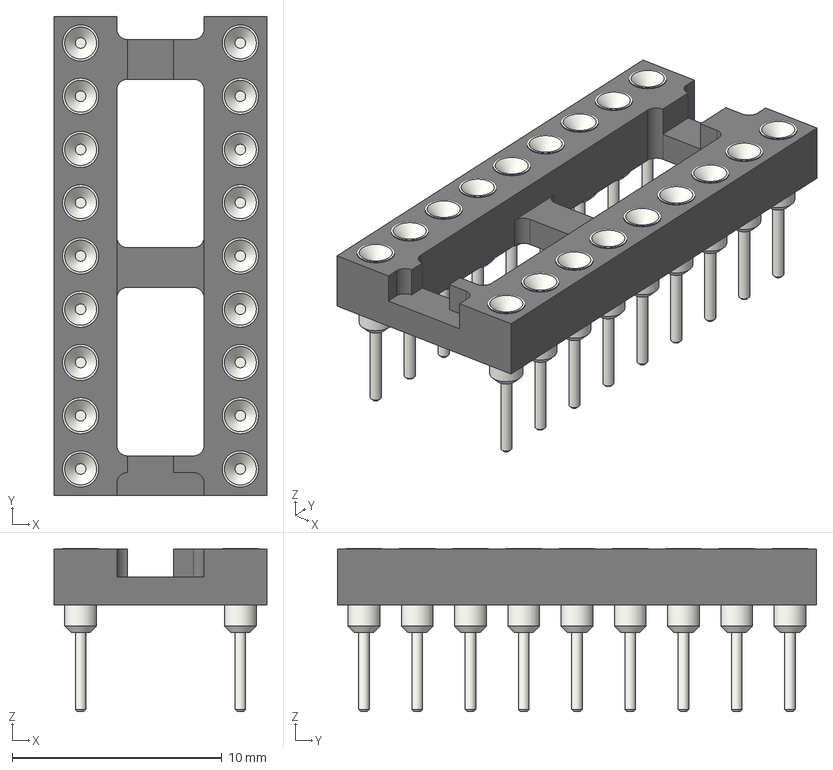
[picture p103: CAD file, 2026-08-16]
STPS/DIP-18_W7.62mm_Socket.step
10.2 x 22.9 x 7.79 mm
