liveboxandy/ZX-Spectrum-48K-Issue-3B---Based-on-Gerbers-by-PABB-on-PCBWay/STPS/DIP-40_W15.24mm_Socket.step

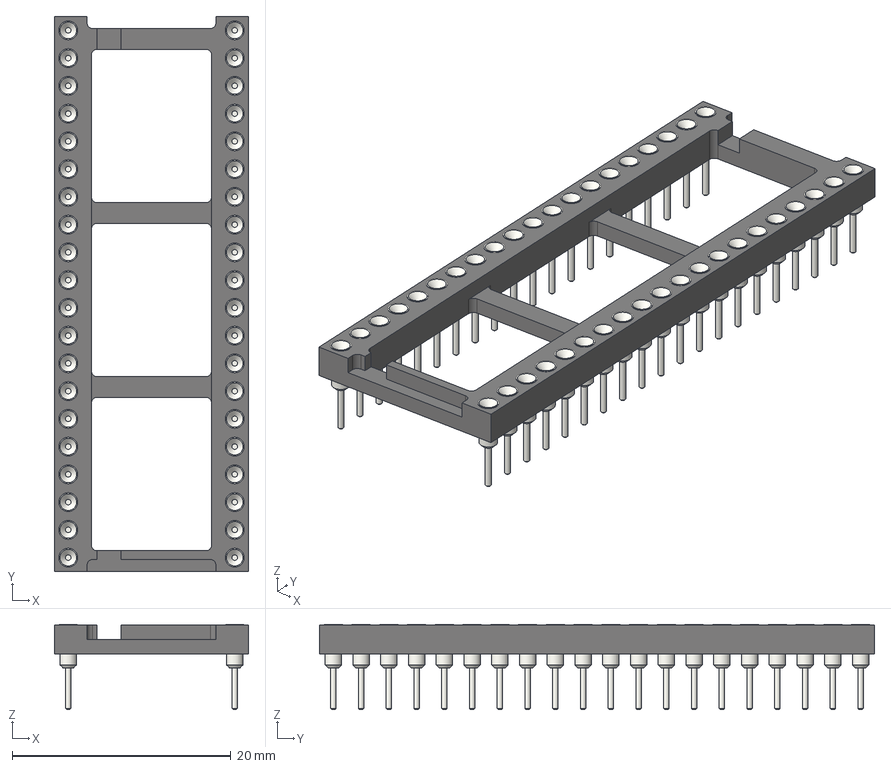
[picture p104: CAD file, 2026-08-16]
STPS/DIP-40_W15.24mm_Socket.step
17.8 x 50.8 x 7.79 mm
