liveboxandy/ZX-Spectrum-48K-Issue-3B---Based-on-Gerbers-by-PABB-on-PCBWay/STPS/BarrelJack_Horizontal.step

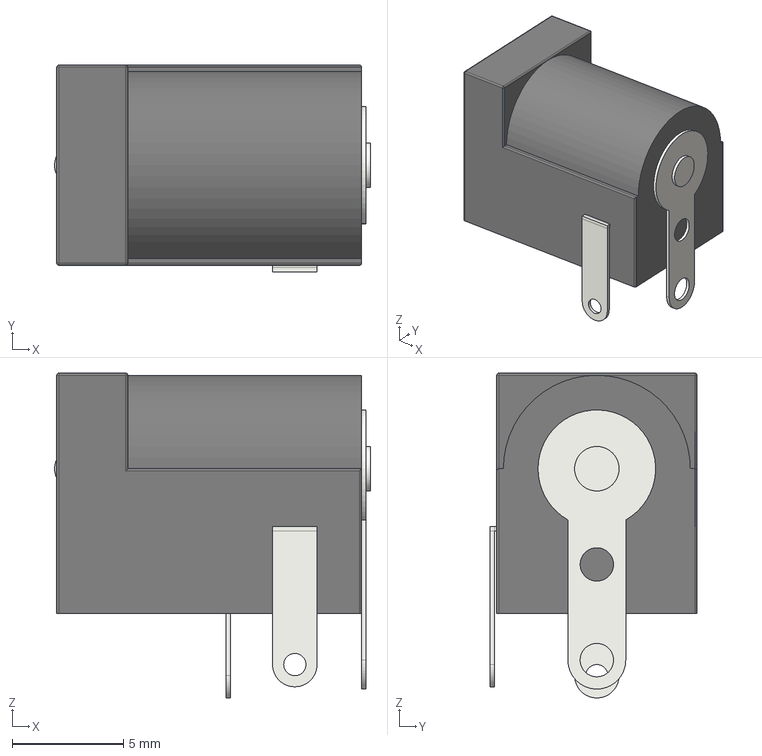
[picture p105: CAD file, 2026-08-16]
STPS/BarrelJack_Horizontal.step
14.2 x 9.30 x 14.6 mm
