liveboxandy/ZX-Spectrum-48K-Issue-3B---Based-on-Gerbers-by-PABB-on-PCBWay/STPS/TO-92Flat.step

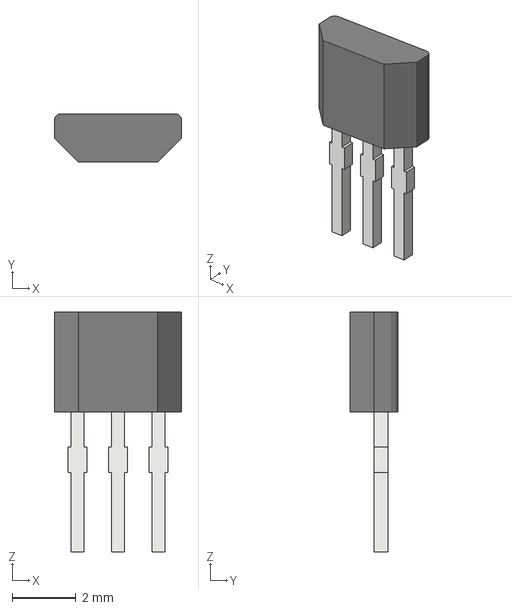
[picture p106: CAD file, 2026-08-16]
STPS/TO-92Flat.step
4.00 x 1.52 x 7.55 mm
