liveboxandy/ZX-Spectrum-48K-Issue-3B---Based-on-Gerbers-by-PABB-on-PCBWay/STPS/UM1233.step

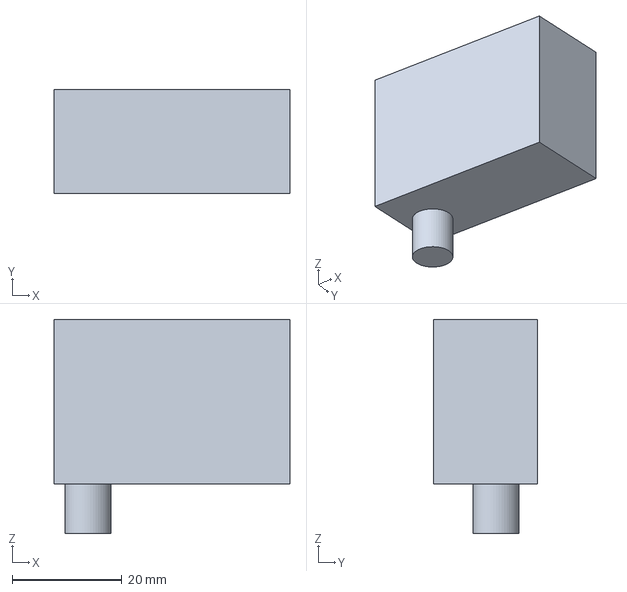
[picture p107: CAD file, 2026-08-16]
STPS/UM1233.step
43.0 x 19.0 x 39.0 mm
